BO55-BO55/NRF-Rc-Controller/CAD/Components/MPU v1.step

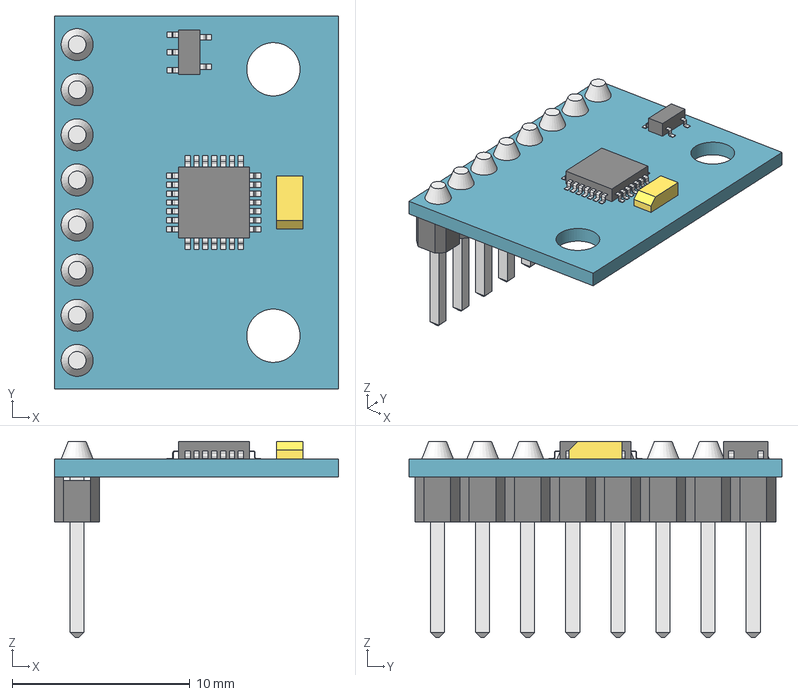
[picture p15: CAD file, 2026-05-26]
CAD/Components/MPU v1.step
16.0 x 21.0 x 11.1 mm
Y
Clone_of_Array
Clone_of_Clone_of_Array
Clone_of_Clone_of_Array001
VCC
GND
SCL
SDA
XDA
XCL
AD0
INT
BotNakama
MPU_1
Cubo001
X
