BO55-BO55/NRF-Rc-Controller/CAD/Components/SPDT-Print-Switch v1.step

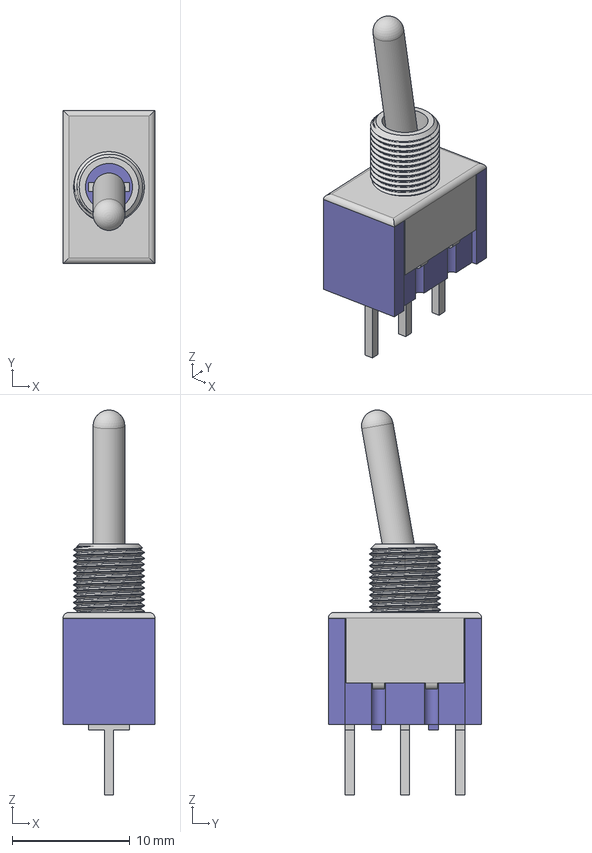
[picture p16: CAD file, 2026-05-26]
CAD/Components/SPDT-Print-Switch v1.step
7.80 x 13.0 x 32.7 mm
Plastic_Housing
Pin2
Pin1
Pin3
Shield
Shaft
