BO55-BO55/NRF-Rc-Controller/CAD/Components/Potentiometer knob_A21x17-PK-AB-K-I v1.step

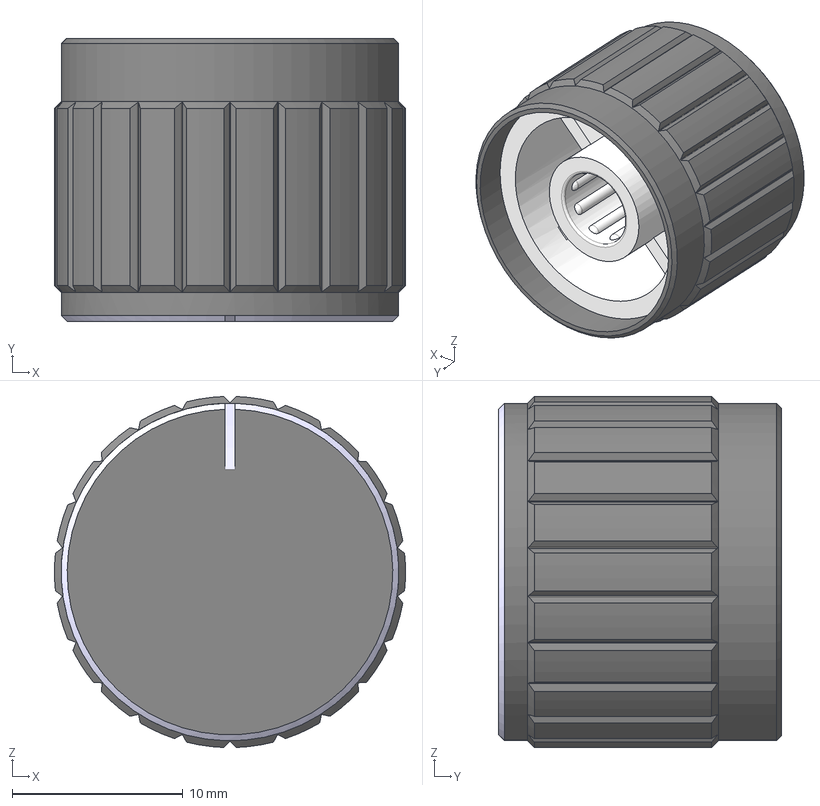
[picture p17: CAD file, 2026-05-26]
CAD/Components/Potentiometer knob_A21x17-PK-AB-K-I v1.step
20.6 x 16.6 x 20.6 mm
