BO55-BO55/NRF-Rc-Controller/CAD/Components/button 6x6 v1.step

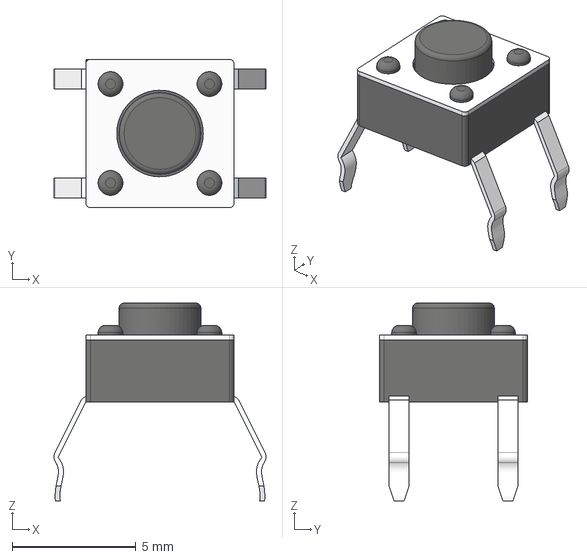
[picture p18: CAD file, 2026-05-26]
CAD/Components/button 6x6 v1.step
8.57 x 6.00 x 8.00 mm
