BO55-BO55/NRF-Rc-Controller/CAD/Components/NRF24L01L+Antenna v2.step

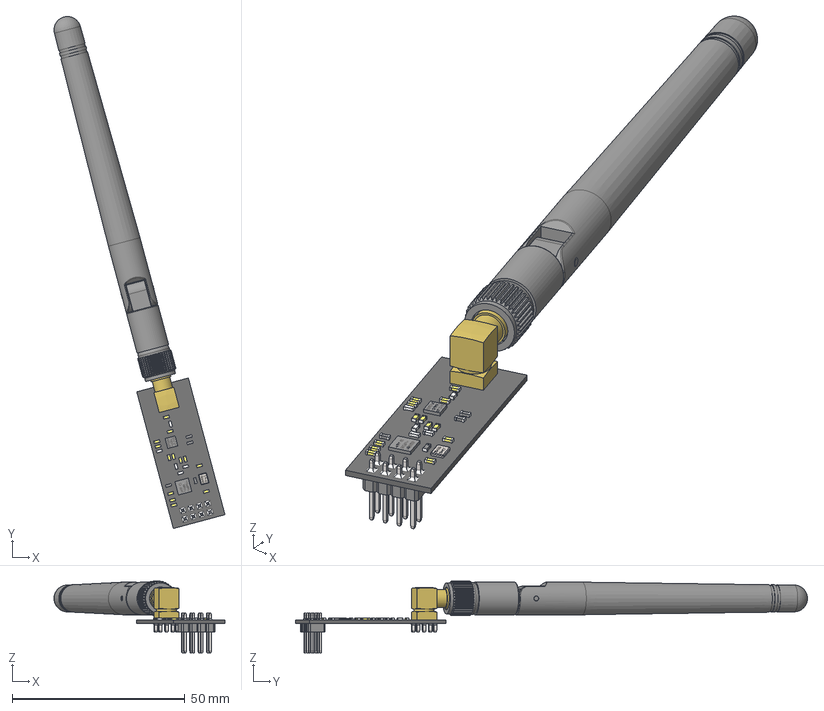
[picture p19: CAD file, 2026-05-26]
CAD/Components/NRF24L01L+Antenna v2.step
49.6 x 148.4 x 20.7 mm
NRF24L01L
Antenna base
Antenna top
